smasa-masas/ckb6/firmware/ckb6/keymaps/vial/config.h

// Copyright 2023 m.ki (@telzo2000)
// SPDX-License-Identifier: GPL-2.0-or-later

#pragma once
#define VIAL_KEYBOARD_UID {0x70, 0xB9, 0xAE, 0x88, 0x0B, 0xEC, 0xA2, 0x36}
#define VIAL_UNLOCK_COMBO_ROWS { 0, 1 }
#define VIAL_UNLOCK_COMBO_COLS { 0, 1 }
